phfbertoleti/shield_hat_RaspLoRaWAN_plus/Imagens/sheild_rasplorawan+_3.jpg

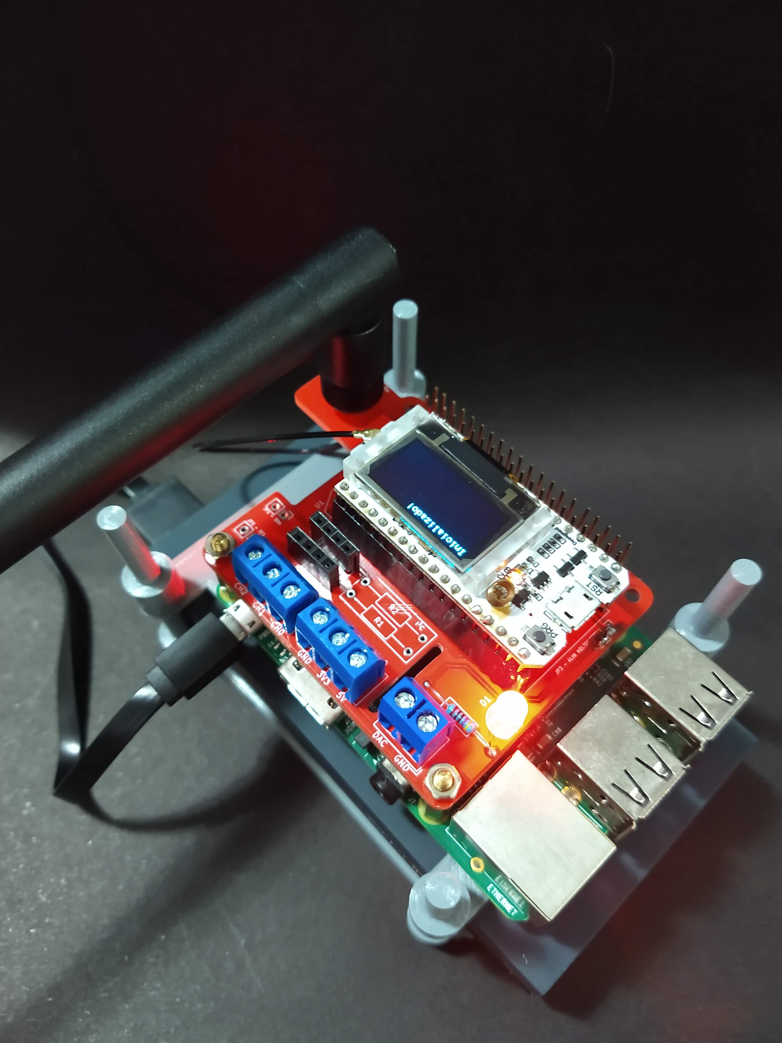
Imagens/sheild_rasplorawan+_3.jpg
