phfbertoleti/shield_hat_RaspLoRaWAN_plus/ESP32/unidade_lorawan/RADIO_LORA_defs.h

/* Header file com as definições do rádio LoRa */
#ifndef RADIO_LORA_DEFS_H
#define RADIO_LORA_DEFS_H

#define GANHO_LORA_DBM          20 //dBm
#define RADIO_RESET_PORT        14
#define RADIO_MOSI_PORT         27
#define RADIO_MISO_PORT         19
#define RADIO_SCLK_PORT         5
#define RADIO_NSS_PORT          18
#define RADIO_DIO_0_PORT        26
#define RADIO_DIO_1_PORT        33
#define RADIO_DIO_2_PORT        32

#endif
