phfbertoleti/shield_hat_RaspLoRaWAN_plus/ESP32/unidade_lorawan/STACKS_SIZE_defs.h

/* Header com definições dos tamanhos das stacks de cada tarefa */
#ifndef STACKS_SIZE_DEFS_H
#define STACKS_SIZE_DEFS_H

#define STACK_SIZE_OLED                  4096
#define STACK_SIZE_LORAWAN               4096
#define STACK_SIZE_STACK_LORAWAN         4096
#define STACK_SIZE_SERIAL_RASPPI         8192

#endif
