phfbertoleti/shield_hat_RaspLoRaWAN_plus/ESP32/unidade_lorawan/SEMAFOROS_defs.h

/* Módulo: header file com os semáforos utilizados no projeto */
#ifndef SEMAFOROS_DEFS_H
#define SEMAFOROS_DEFS_H

#define TICKS_ESPERA_SEMAFORO_SERIAL        ( TickType_t ) 1000

SemaphoreHandle_t xSerial_semaphore;

#endif
