phfbertoleti/shield_hat_RaspLoRaWAN_plus/ESP32/unidade_lorawan/maquina_estados_defs.h

/* Header file com as definições da maquina de estados de recepção */
#ifndef MAQ_ESTADOS_RECEPCAO_DEFS_H
#define MAQ_ESTADOS_RECEPCAO_DEFS_H

/* Definições - estados */
#define ESTADO_BYTE_SINCRONIA_1                0x00
#define ESTADO_BYTE_SINCRONIA_2                0x01
#define ESTADO_BYTE_SINCRONIA_3                0x02
#define ESTADO_BYTE_SINCRONIA_4                0x03
#define ESTADO_BYTE_SINCRONIA_5                0x04
#define ESTADO_BYTE_SINCRONIA_6                0x05
#define ESTADO_RECEBE_TIPO_DE_DADOS            0x06
#define ESTADO_RECEBE_TAMANHO                  0x07
#define ESTADO_RECEBE_DADOS                    0x08
#define ESTADO_AGUARDA_DADOS_VERIFICA_CKS      0x09

/* Variável que armazena estado da máquina de estados de reepção */
char estado_recepcao = ESTADO_BYTE_SINCRONIA_1;

#endif
