phfbertoleti/shield_hat_RaspLoRaWAN_plus/Raspberry/recebe_envia_dados_uart/dados_defs.h

/* Header file com as definições dos dados a receber e a enviar 
* Autor: Pedro Bertoleti 
*/
#ifndef DADOS_REC_ENV_DEFS_H
#define DADOS_REC_ENV_DEFS_H

/* Definição - tamanho máximo do array de dados (escrita e leitura) */
#define TAMANHO_ARRAY_DADOS            255

#endif
