phfbertoleti/shield_hat_RaspLoRaWAN_plus/Raspberry/recebe_envia_dados_uart/debug_defs.h

/* Header file com as definições de debug 
* Autor: Pedro Bertoleti 
*/
#ifndef DEBUG_DEFS_H
#define DEBUG_DEFS_H

/* Descomente a linha abaixo para habilitar o debug verboso */
#define HABILITA_DEBUG_VIA_PRINTF

#endif
